stav98/EEKYP/Subsystem1_Irrigation/software/avr/readme.md

Εδώ υπάρχει όλος ο πηγαίος κώδικας για την πλακέτα του Arduino Nano.
IDE VsCode, PlatformIO
