stav98/EEKYP/Subsystem1_Irrigation/software/esp8266/readme.md

Εδώ υπάρχει όλος ο πηγαίος κώδικας για την πλακέτα ESP01 με τον ESP8266.
Η μνήμη flash χωρίζεται σε δύο μέρη. Το 1ο έχει το firmware ενώ το 2ο είναι το filesystem σε LittleFS για ανέβασμα των αρχείων HTML.
IDE VsCode, PlatformIO
