stav98/EEKYP/Subsystem1_Irrigation/3D/valve_body.jpg

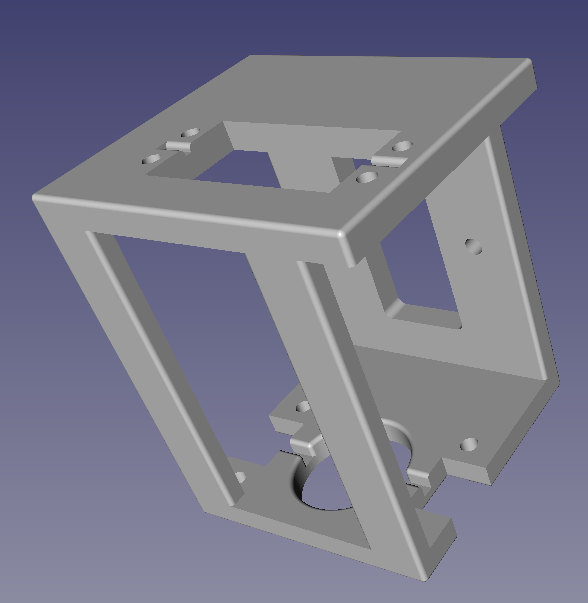
Subsystem1_Irrigation/3D/valve_body.jpg
