stav98/EEKYP/Subsystem1_Irrigation/3D/valve_rotor.jpg

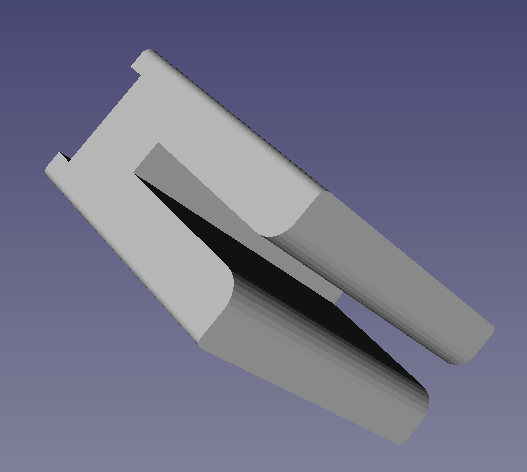
Subsystem1_Irrigation/3D/valve_rotor.jpg
