stav98/EEKYP/Subsystem1_Irrigation/Images/EEKYP1_scr1.png

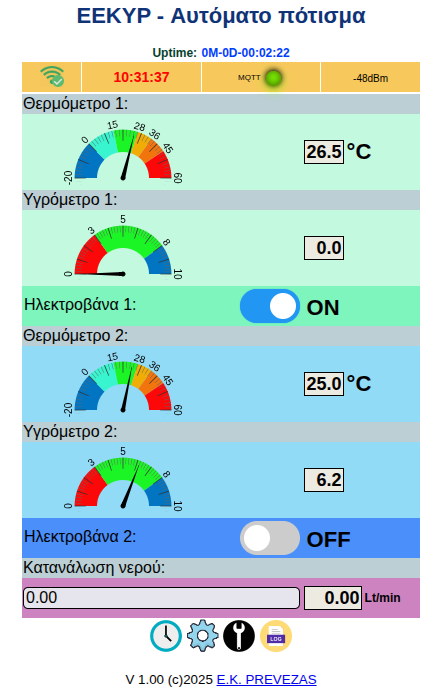
Subsystem1_Irrigation/Images/EEKYP1_scr1.png
