stav98/EEKYP/Subsystem1_Irrigation/Images/EEKYP_team.jpg

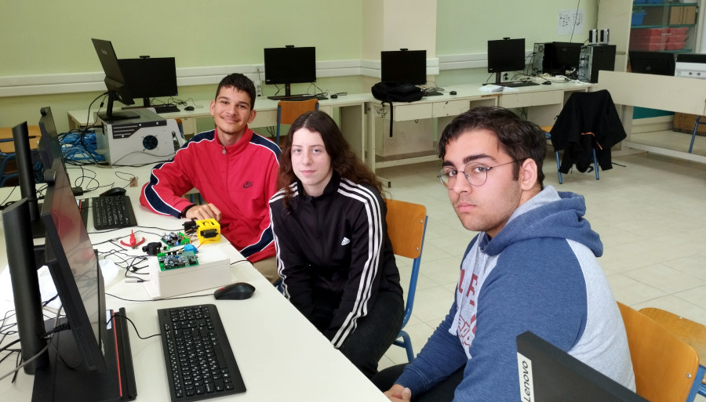
Subsystem1_Irrigation/Images/EEKYP_team.jpg
