stav98/EEKYP/Subsystem1_Irrigation/schematics/Soil-Moisture-Sensor-Module-Schematic.png

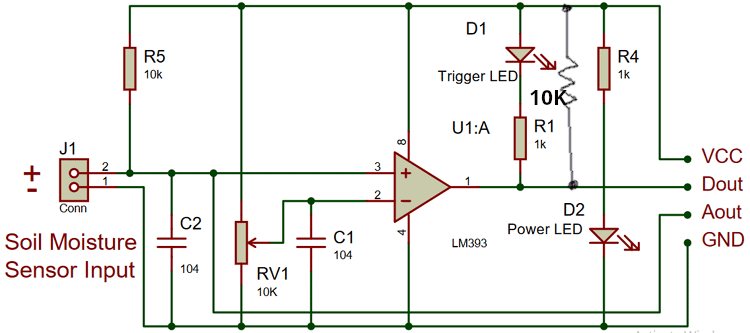
Subsystem1_Irrigation/schematics/Soil-Moisture-Sensor-Module-Schematic.png
