stav98/EEKYP/Subsystem2_PowerSaving/Images/EEKYP2_scr1.png

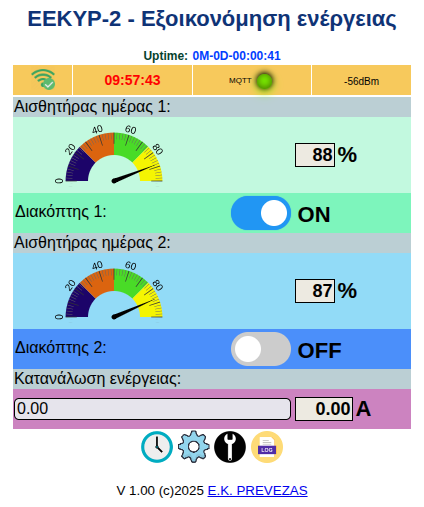
Subsystem2_PowerSaving/Images/EEKYP2_scr1.png
