stav98/EEKYP/Subsystem2_PowerSaving/Images/EEKYP2_scr3.png

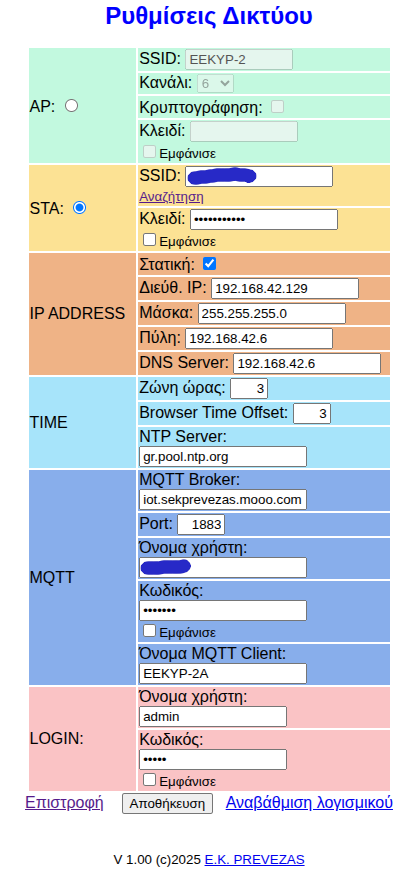
Subsystem2_PowerSaving/Images/EEKYP2_scr3.png
