stav98/EEKYP/Subsystem2_PowerSaving/schematics/current-sensor-circuit.jpg

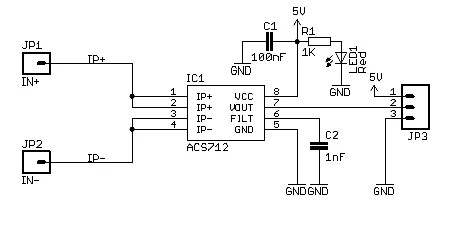
Subsystem2_PowerSaving/schematics/current-sensor-circuit.jpg
