stav98/EEKYP/Subsystem3_WeatherStation/3D/Rainfall meter _ Rain gauge/images/2cdfe765d356b9783a792a951a1a0e3f.png

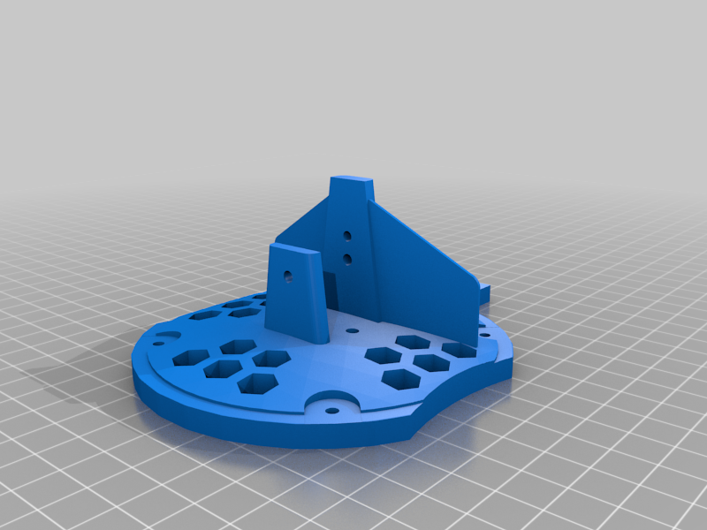
Subsystem3_WeatherStation/3D/Rainfall meter _ Rain gauge/images/2cdfe765d356b9783a792a951a1a0e3f.png
