stav98/EEKYP/Subsystem3_WeatherStation/3D/Rainfall meter _ Rain gauge/images/3b38dc10710fc57b048369caf85057be.png

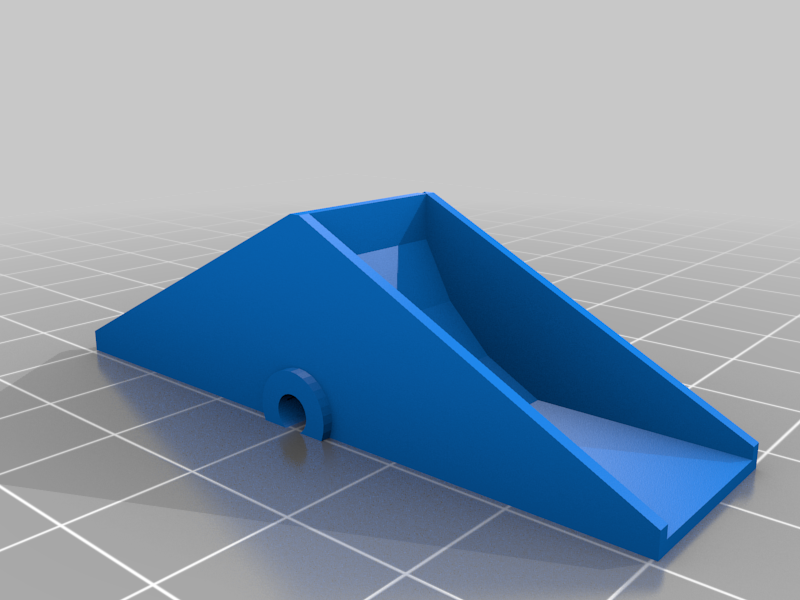
Subsystem3_WeatherStation/3D/Rainfall meter _ Rain gauge/images/3b38dc10710fc57b048369caf85057be.png
