stav98/EEKYP/Subsystem3_WeatherStation/3D/Rainfall meter _ Rain gauge/images/668c7d044ce66c4b228c590e39a806a0.png

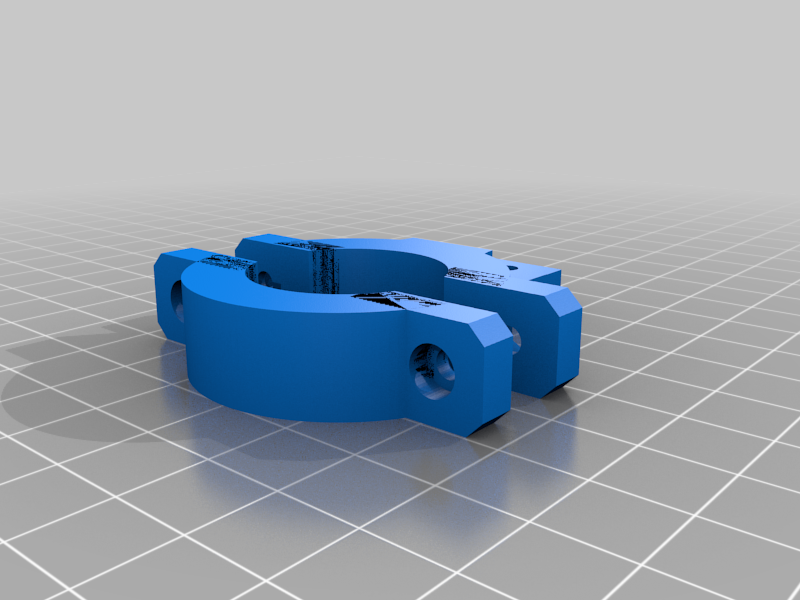
Subsystem3_WeatherStation/3D/Rainfall meter _ Rain gauge/images/668c7d044ce66c4b228c590e39a806a0.png
