stav98/EEKYP/Subsystem3_WeatherStation/3D/Rainfall meter _ Rain gauge/images/2019-07-26_17.47.01.jpg

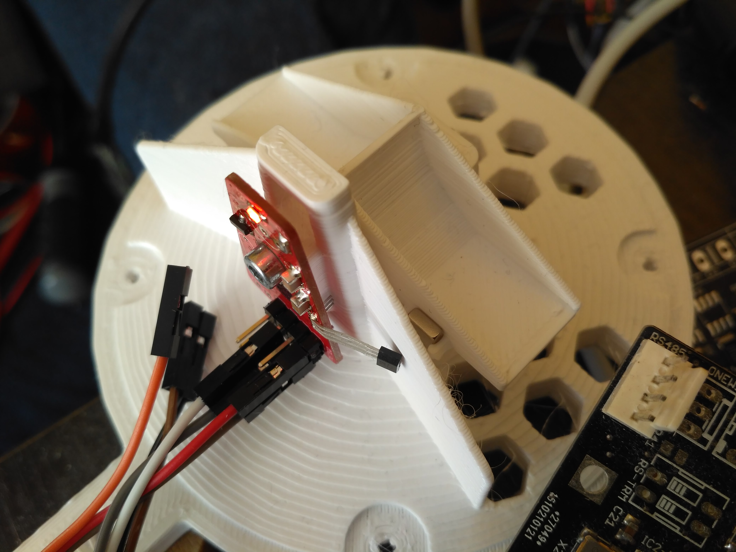
Subsystem3_WeatherStation/3D/Rainfall meter _ Rain gauge/images/2019-07-26_17.47.01.jpg
