stav98/EEKYP/Subsystem3_WeatherStation/3D/Rainfall meter _ Rain gauge/images/2019-07-28_15.31.44.jpg

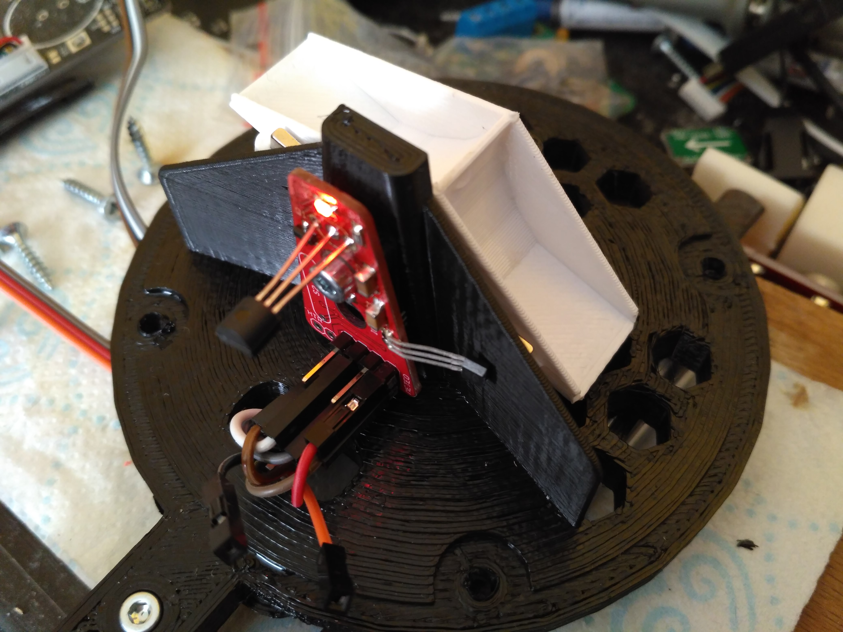
Subsystem3_WeatherStation/3D/Rainfall meter _ Rain gauge/images/2019-07-28_15.31.44.jpg
