stav98/EEKYP/Subsystem3_WeatherStation/3D/Rainfall meter _ Rain gauge/images/2019-07-29_14.39.09.jpg

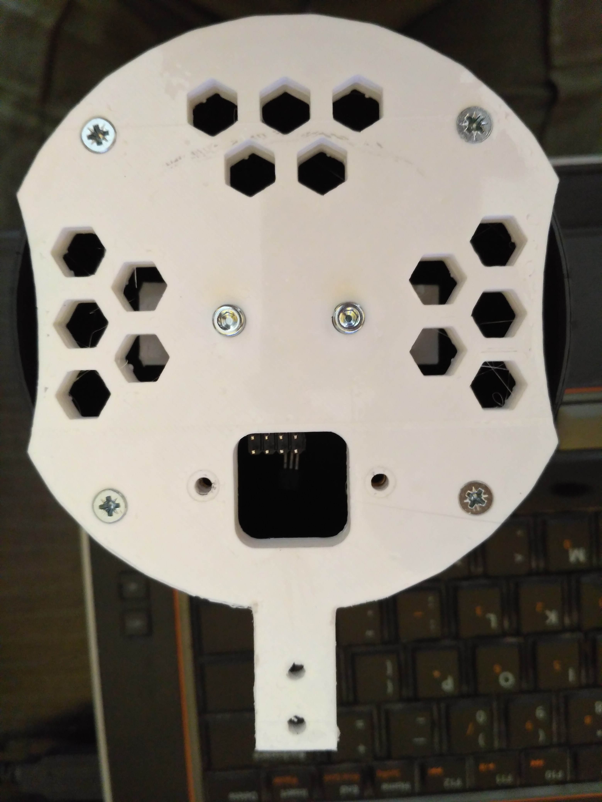
Subsystem3_WeatherStation/3D/Rainfall meter _ Rain gauge/images/2019-07-29_14.39.09.jpg
