stav98/EEKYP/Subsystem3_WeatherStation/3D/Rainfall meter _ Rain gauge/images/2019-07-29_18.38.01.jpg

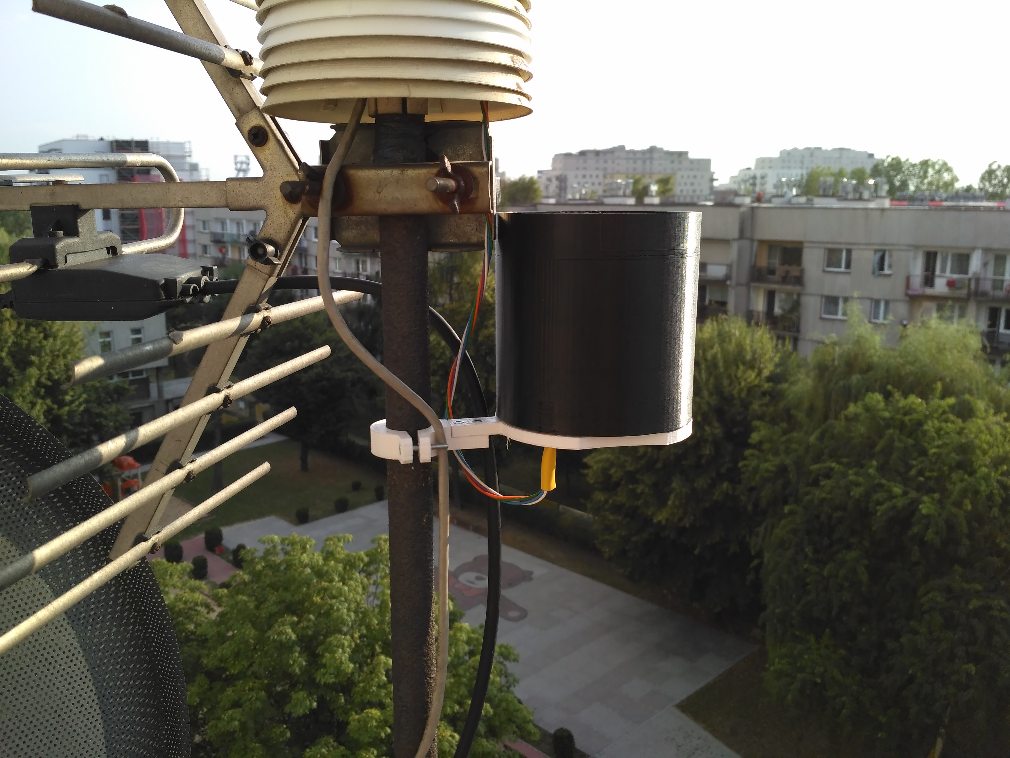
Subsystem3_WeatherStation/3D/Rainfall meter _ Rain gauge/images/2019-07-29_18.38.01.jpg
