stav98/EEKYP/Subsystem3_WeatherStation/3D/Rainfall meter _ Rain gauge/images/7200743348170216a2c66e8219aefd83.png

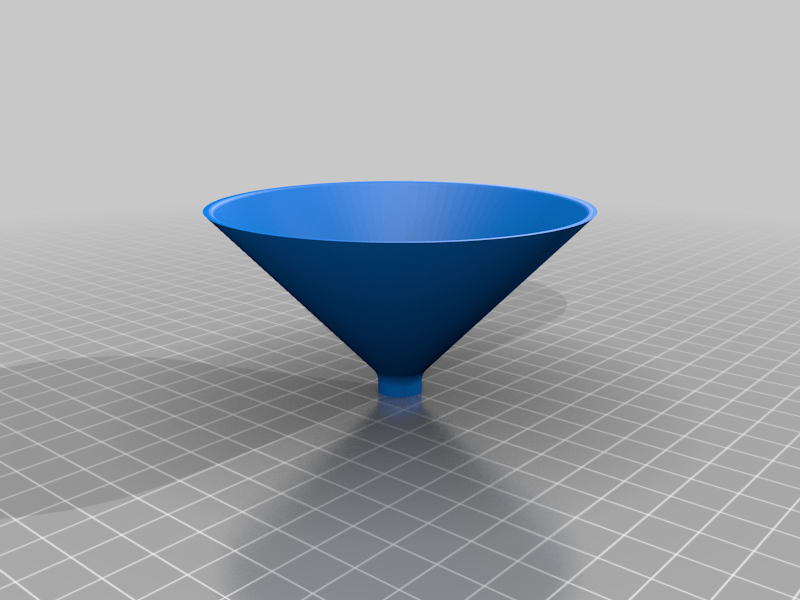
Subsystem3_WeatherStation/3D/Rainfall meter _ Rain gauge/images/7200743348170216a2c66e8219aefd83.png
