stav98/EEKYP/Subsystem3_WeatherStation/3D/Rainfall meter _ Rain gauge/images/Screenshot_2019-07-30_09.27.33.png

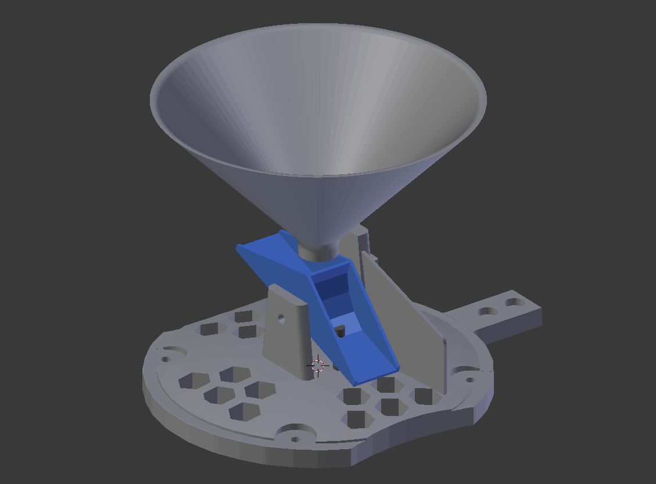
Subsystem3_WeatherStation/3D/Rainfall meter _ Rain gauge/images/Screenshot_2019-07-30_09.27.33.png
