stav98/EEKYP/Subsystem3_WeatherStation/images/weather_system2.jpg

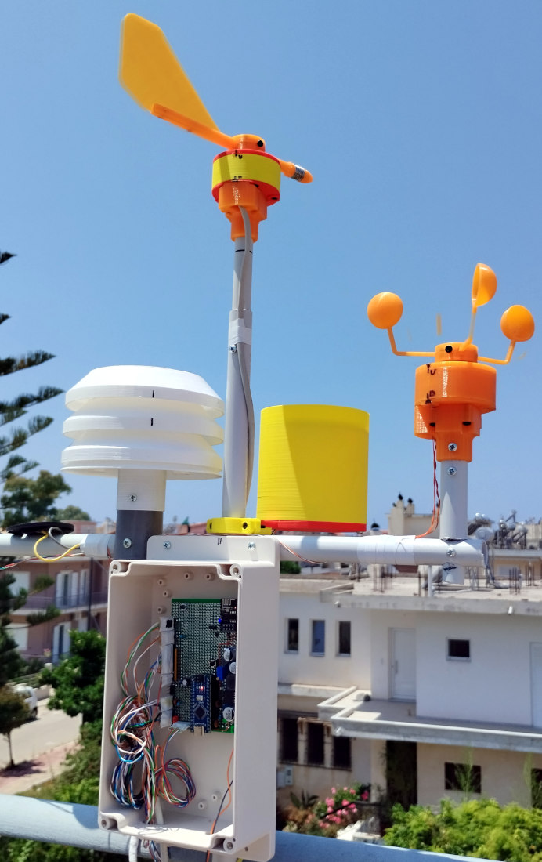
Subsystem3_WeatherStation/images/weather_system2.jpg
