stav98/EEKYP/Subsystem4_NodeRed/images/EEKYP4_S2_scr1.png

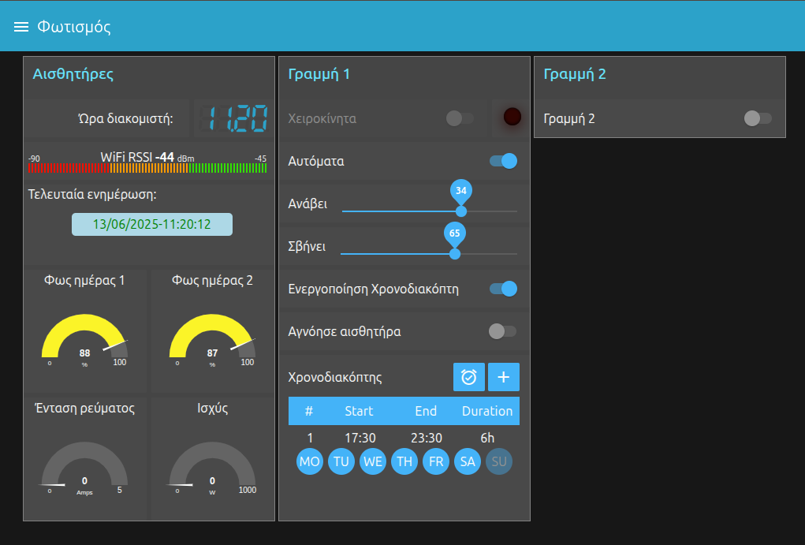
Subsystem4_NodeRed/images/EEKYP4_S2_scr1.png
