stav98/EEKYP/Subsystem3_WeatherStation/3D/Rainfall meter _ Rain gauge/files/pole-holder.stl

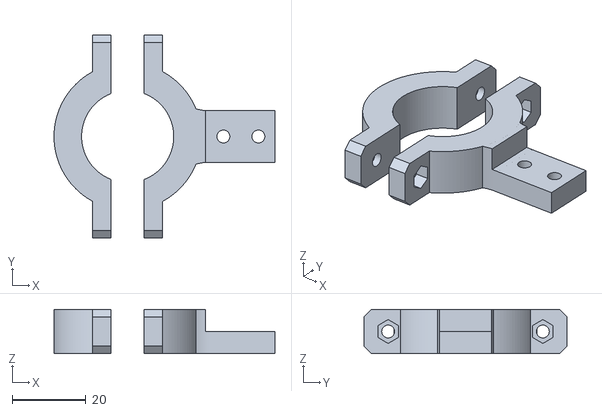
[picture p95: CAD file, 2025-05-21]
Subsystem3_WeatherStation/3D/Rainfall meter _ Rain gauge/files/pole-holder.stl
60.0 x 55.0 x 12.0
