stav98/EEKYP/Subsystem3_WeatherStation/3D/Wind_vane/8_led_holder(x2).STL

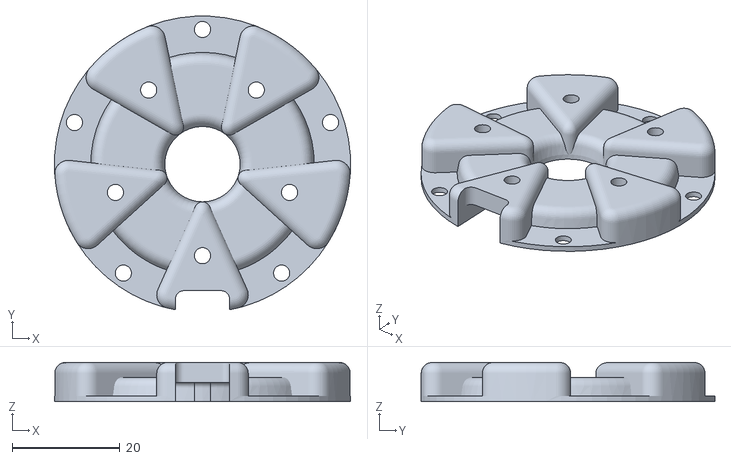
[picture p96: CAD file, 2025-03-21]
Subsystem3_WeatherStation/3D/Wind_vane/8_led_holder(x2).STL
55.0 x 54.5 x 7.25
