stav98/EEKYP/Subsystem3_WeatherStation/3D/Anemometer - 41367/files/body_bottom.STL

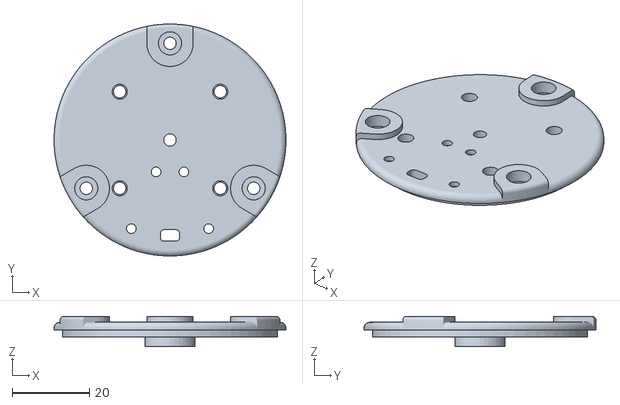
[picture p97: CAD file, 2025-03-21]
Subsystem3_WeatherStation/3D/Anemometer - 41367/files/body_bottom.STL
60.0 x 60.0 x 7.80
