stav98/EEKYP/Subsystem3_WeatherStation/3D/Rainfall meter _ Rain gauge/files/rainfall-meter-bucket-mag.stl

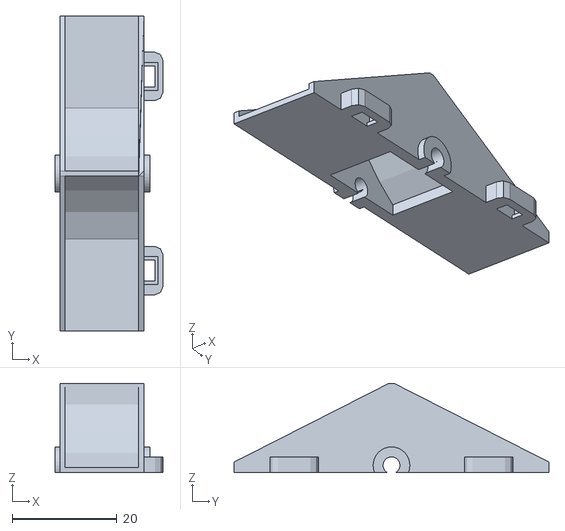
[picture p98: CAD file, 2025-05-21]
Subsystem3_WeatherStation/3D/Rainfall meter _ Rain gauge/files/rainfall-meter-bucket-mag.stl
20.5 x 60.0 x 17.0
