stav98/EEKYP/Subsystem3_WeatherStation/3D/Wind_vane/2_body_top.STL

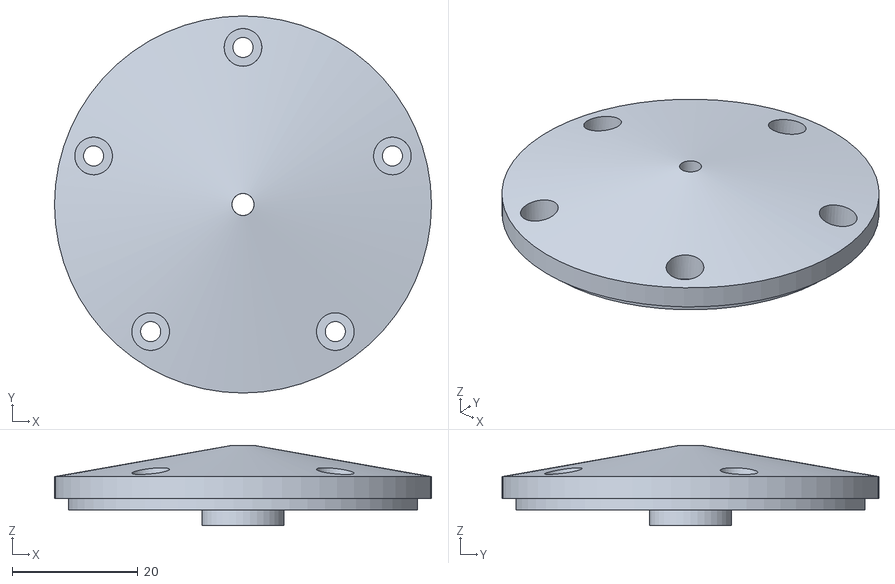
[picture p99: CAD file, 2025-03-21]
Subsystem3_WeatherStation/3D/Wind_vane/2_body_top.STL
60.0 x 60.0 x 12.8
