stav98/EEKYP/Subsystem3_WeatherStation/3D/Anemometer - 41367/files/cupx3.STL

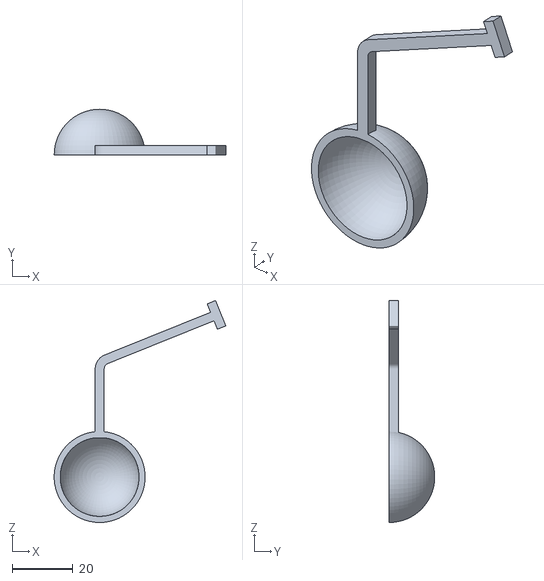
[picture p100: CAD file, 2025-03-21]
Subsystem3_WeatherStation/3D/Anemometer - 41367/files/cupx3.STL
56.6 x 15.0 x 73.2
