stav98/EEKYP/Subsystem3_WeatherStation/3D/Wind_vane/5_noze.STL

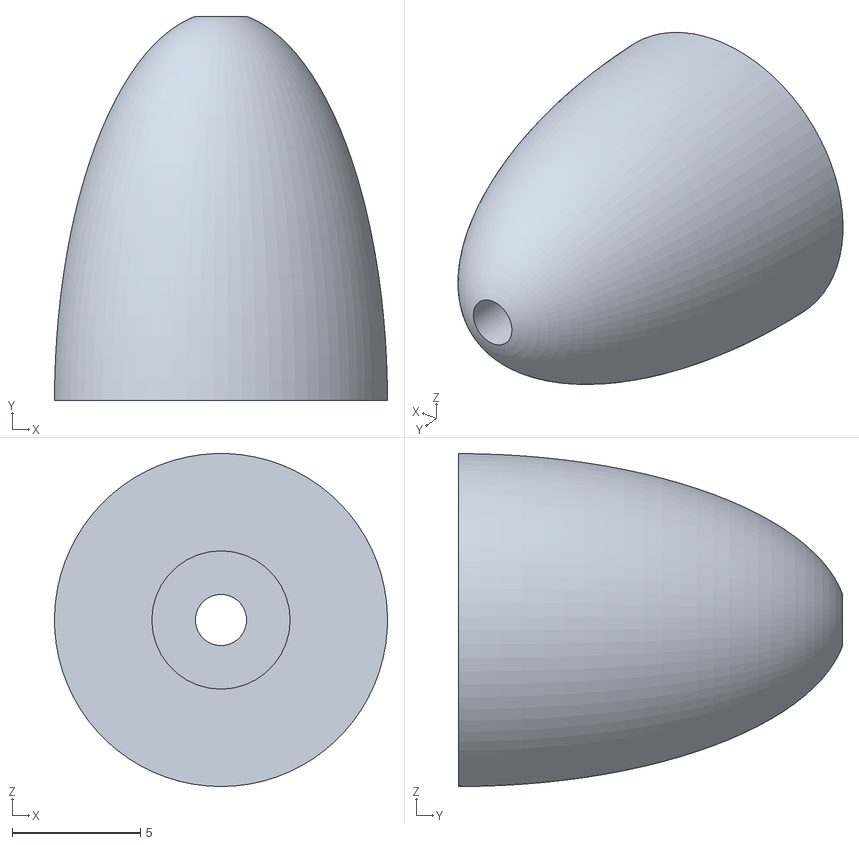
[picture p101: CAD file, 2025-03-21]
Subsystem3_WeatherStation/3D/Wind_vane/5_noze.STL
13.0 x 15.0 x 13.0
