stav98/EEKYP/Subsystem3_WeatherStation/3D/Anemometer - 41367/files/rotor_lockx2.STL

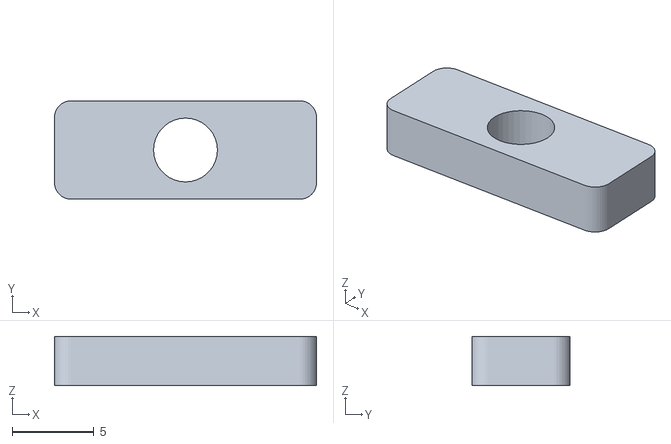
[picture p102: CAD file, 2025-03-21]
Subsystem3_WeatherStation/3D/Anemometer - 41367/files/rotor_lockx2.STL
16.0 x 6.00 x 3.00
