stav98/EEKYP/Subsystem3_WeatherStation/3D/Wind_vane/10_hub_bottom.STL

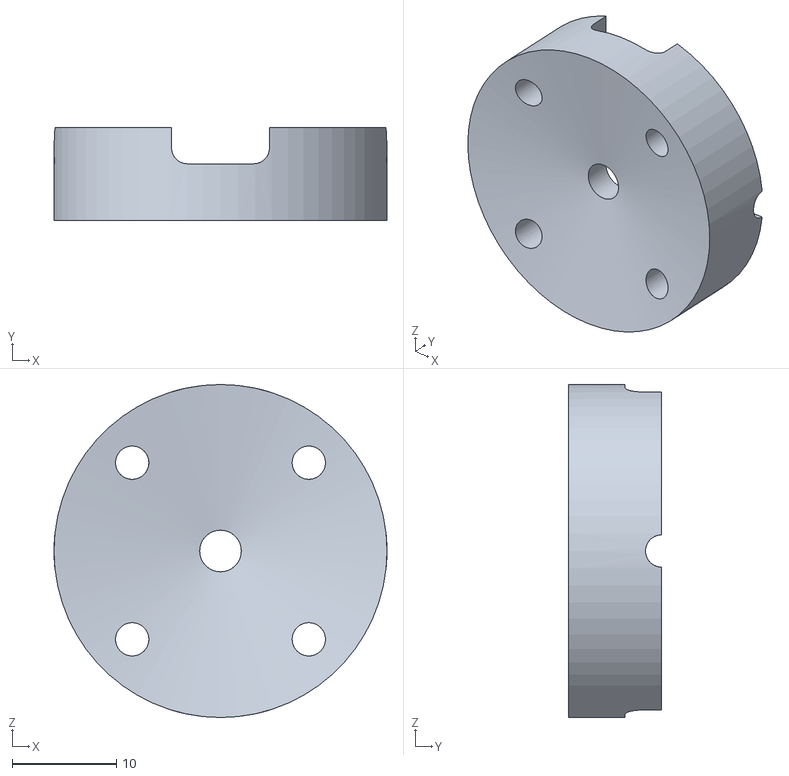
[picture p103: CAD file, 2025-03-21]
Subsystem3_WeatherStation/3D/Wind_vane/10_hub_bottom.STL
32.0 x 8.97 x 32.0
