stav98/EEKYP/Subsystem3_WeatherStation/3D/Wind_vane/9_hub_top.STL

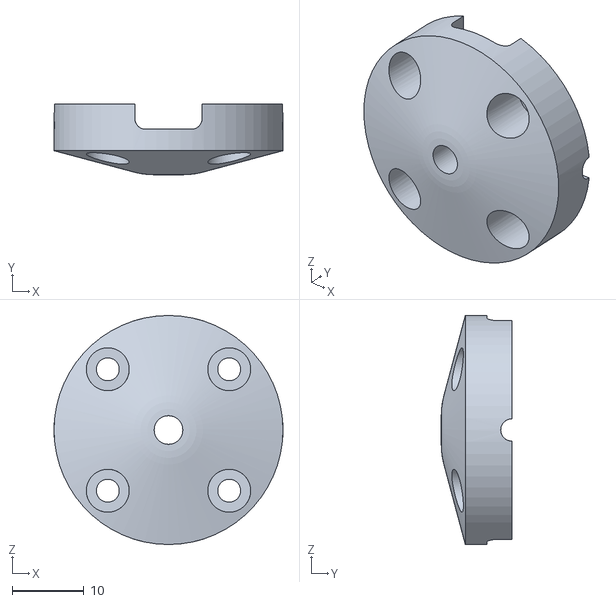
[picture p104: CAD file, 2025-03-21]
Subsystem3_WeatherStation/3D/Wind_vane/9_hub_top.STL
32.0 x 9.87 x 32.0
