stav98/EEKYP/Subsystem3_WeatherStation/3D/Anemometer - 41367/files/rotor_part1.STL

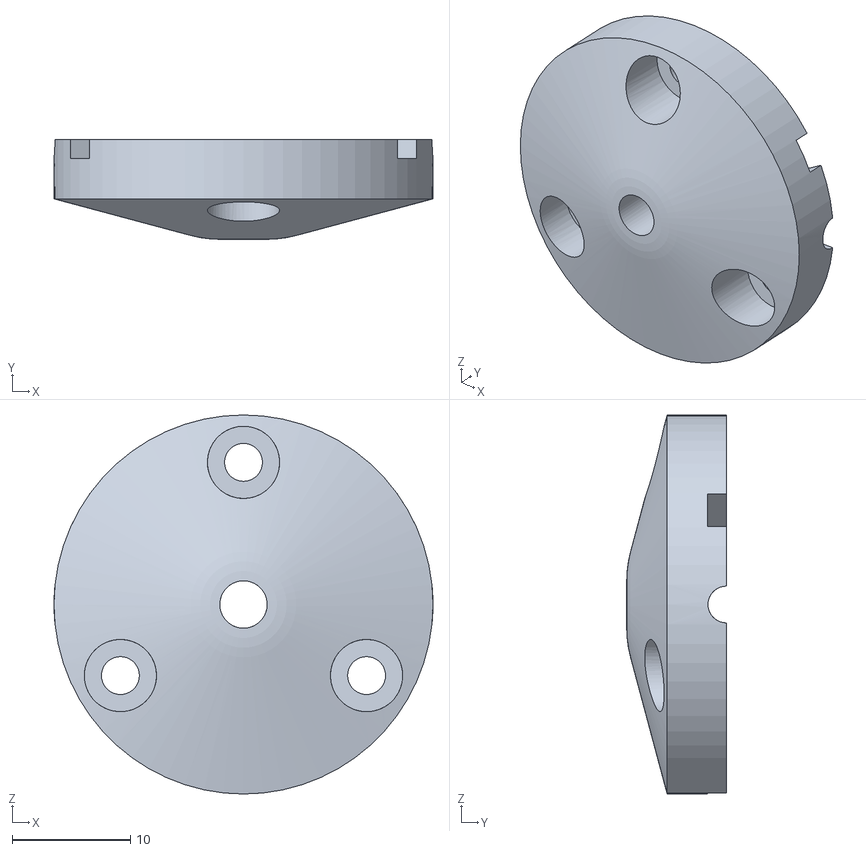
[picture p105: CAD file, 2025-03-21]
Subsystem3_WeatherStation/3D/Anemometer - 41367/files/rotor_part1.STL
32.0 x 8.42 x 32.0
