stav98/EEKYP/Subsystem3_WeatherStation/3D/Wind_vane/4_wheel.STL

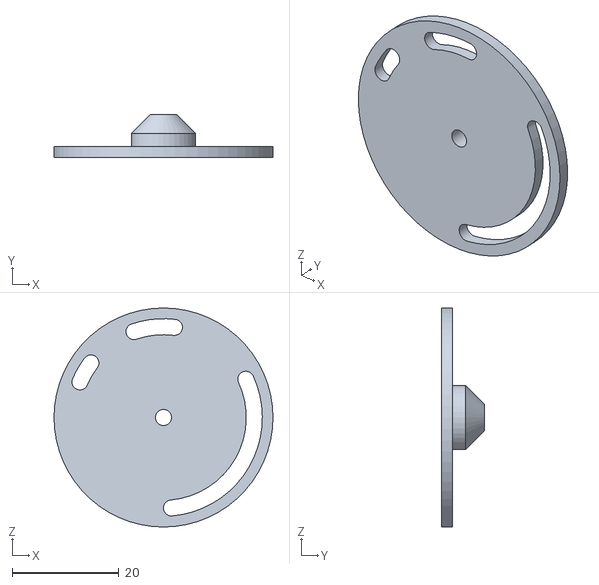
[picture p106: CAD file, 2025-03-21]
Subsystem3_WeatherStation/3D/Wind_vane/4_wheel.STL
41.0 x 8.00 x 41.0
