stav98/EEKYP/Subsystem3_WeatherStation/3D/Anemometer - 41367/files/led_holderx2.STL

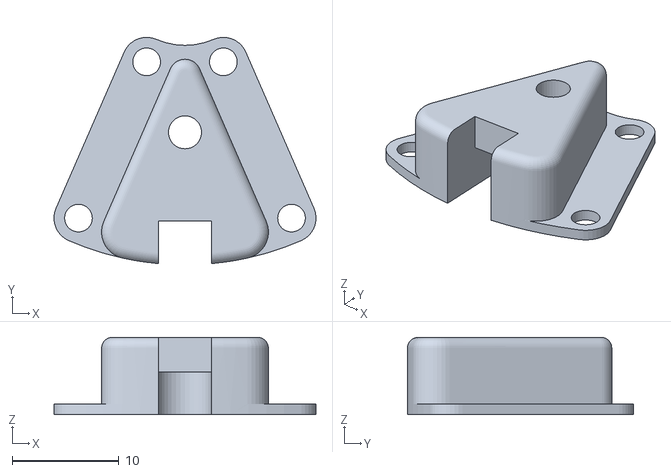
[picture p107: CAD file, 2025-03-21]
Subsystem3_WeatherStation/3D/Anemometer - 41367/files/led_holderx2.STL
24.6 x 21.2 x 7.25
