stav98/EEKYP/Subsystem3_WeatherStation/3D/Wind_vane/3_body_bottom.STL

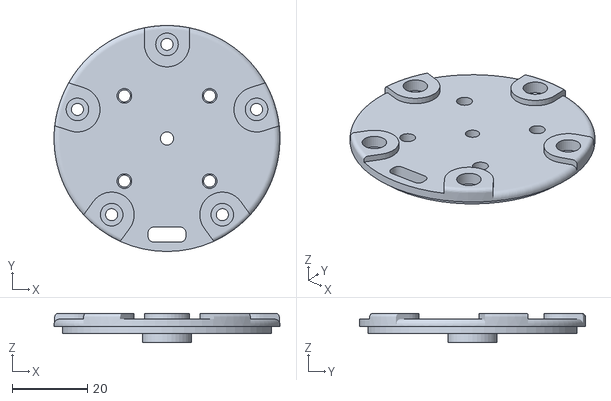
[picture p108: CAD file, 2025-03-21]
Subsystem3_WeatherStation/3D/Wind_vane/3_body_bottom.STL
60.0 x 60.0 x 7.80
