stav98/EEKYP/Subsystem3_WeatherStation/3D/Wind_vane/How to measure wind_ (part 2)_files/fleche_complete_1.jpg

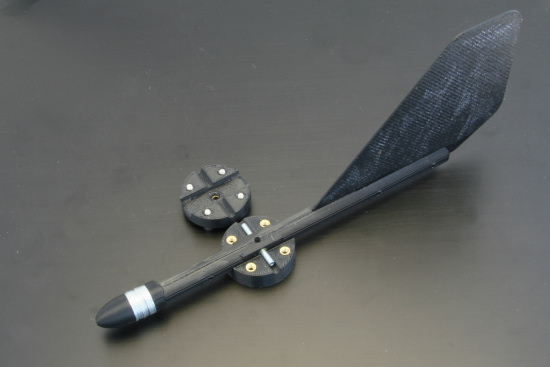
Subsystem3_WeatherStation/3D/Wind_vane/How to measure wind_ (part 2)_files/fleche_complete_1.jpg
