stav98/EEKYP/Subsystem3_WeatherStation/3D/Wind_vane/How to measure wind_ (part 2)_files/girouette_wiring_1.png

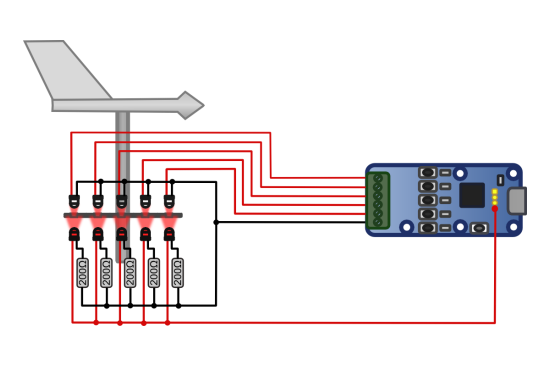
Subsystem3_WeatherStation/3D/Wind_vane/How to measure wind_ (part 2)_files/girouette_wiring_1.png
