stav98/EEKYP/Subsystem3_WeatherStation/3D/Wind_vane/How to measure wind_ (part 2)_files/inserts_3.jpg

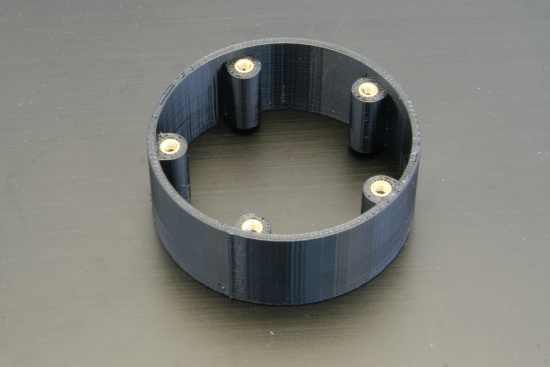
Subsystem3_WeatherStation/3D/Wind_vane/How to measure wind_ (part 2)_files/inserts_3.jpg
