stav98/EEKYP/Subsystem3_WeatherStation/images/anemometer_assembled.jpg

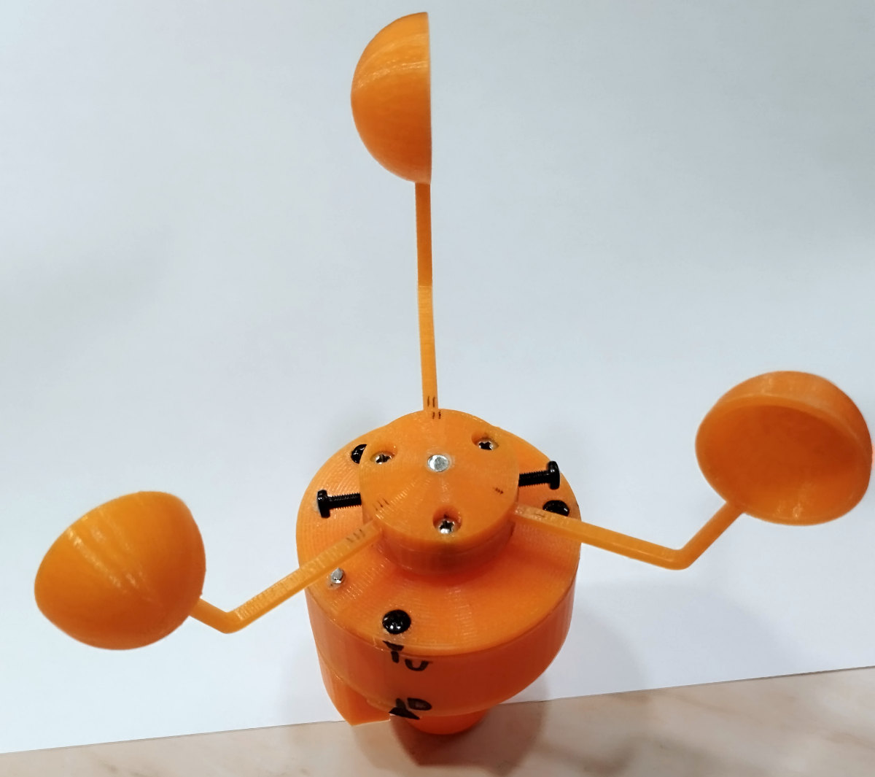
Subsystem3_WeatherStation/images/anemometer_assembled.jpg
