stav98/EEKYP/Subsystem3_WeatherStation/software/avr/EEKYP3_AVR/src/buttons.h

#define PULL_UP     HIGH
void SetupButtons(void);
void But_Click(void);
void But_Long_Click(void);
void But_Dbl_Click(void);

class Buttons
{
 private:
   int _pin;

    // Properties //
   ////////////////

   // Debounce period to prevent flickering when pressing or releasing the button (in ms)
   int Debounce;
   // Max period between clicks for a double click event (in ms)
   int DblClickDelay;
   // Hold period for a long press event (in ms)
   int LongPressDelay;

    // Variables //
   ///////////////

   // Value read from button
   boolean state;
   // Last value of button state
   boolean _lastState;
   // whether we're waiting for a double click (down)
   boolean _dblClickWaiting;
   // whether to register a double click on next release, or whether to wait and click
   boolean _dblClickOnNextUp;
   // whether it's OK to do a single click
   boolean _singleClickOK;

   // time the button was pressed down
   long _downTime;
   // time the button was released
   long _upTime;

   // whether to ignore the button release because the click+hold was triggered
   boolean _ignoreUP;
   // when held, whether to wait for the up event
   boolean _waitForUP;
   // whether or not the hold event happened already
   boolean _longPressHappened;

 public:
   void (*OnClick)(void);
   void (*OnDblClick)(void);
   void (*OnLongPress)(void);

 Buttons()
     {
      // Initialization of properties
      Debounce = 30;
      DblClickDelay = 300; //300
      LongPressDelay = 5000;

      // Initialization of variables
      state = true;
      _lastState = true;
      _dblClickWaiting = false;
      _dblClickOnNextUp = false;
      _singleClickOK = false; //Default = true
      _downTime = -1;
      _upTime = -1;
      _ignoreUP = false;
      _waitForUP = false;
      _longPressHappened = false;
     }

   void Configure(int pin)
      {
       _pin = pin;
       pinMode(_pin, INPUT_PULLUP); //Κάνε το pin είσοδο Pull Up
      }

   void CheckBP(void)
      {
       int resultEvent = 0;
       long millisRes = millis();
       state = digitalRead(_pin);
       //---- Κουμπί πατήθηκε ----
       if (state != PULL_UP && _lastState == PULL_UP  && (millisRes - _upTime) > Debounce)
          {
           //Serial.println("button down"); //Debug
           _downTime = millisRes;
           _ignoreUP = false;
           _waitForUP = false;
           _singleClickOK = true;
           _longPressHappened = false;
           if ((millisRes - _upTime) < DblClickDelay && _dblClickOnNextUp == false && _dblClickWaiting == true)
               _dblClickOnNextUp = true;
           else
               _dblClickOnNextUp = false;
           _dblClickWaiting = false;
          }
       // Button released
       else if (state == PULL_UP && _lastState != PULL_UP && (millisRes - _downTime) > Debounce)
          {
           //Serial.println("button up");
           if (_ignoreUP == false) //Replace "(!_ignoreUP)" by "(not _ignoreUP)"
              {
               _upTime = millisRes;
               if (_dblClickOnNextUp == false)
                   _dblClickWaiting = true;
               else
                  {
                   resultEvent = 2;
                   _dblClickOnNextUp = false;
                   _dblClickWaiting = false;
                   _singleClickOK = false;
                  }
              }
          }

       // Test for normal click event: DblClickDelay expired
       if (state == PULL_UP && (millisRes - _upTime) >= DblClickDelay && _dblClickWaiting == true && _dblClickOnNextUp == false && _singleClickOK == true && resultEvent != 2)
          {
           resultEvent = 1;
           _dblClickWaiting = false;
          }

       //----- Έλεγχος για παρατεταμένο πάτημα -----
       //Είναι πατημένο και ο χρόνος πέρασε την καθυστέρηση του LongPressDelay
       if (state != PULL_UP && (millisRes - _downTime) >= LongPressDelay)
          {
           //Πυροδότησε το παρατεταμένο πάτημα
           // Αν δεν πατήθηκε πριν παρατεταμένα
           if (_longPressHappened == false)
              {
               resultEvent = 3;
               _waitForUP = true;
               _ignoreUP = true;
               _dblClickOnNextUp = false;
               _dblClickWaiting = false;
               _downTime = millis(); //ισως δεν χρειάζεται
               _longPressHappened = true;
              }
          }
       _lastState = state;
       //if (resultEvent!=0)
       //  Serial.println((String)"resultEvent: " + (String) resultEvent);

       if (resultEvent == 1 && OnClick) OnClick();
       if (resultEvent == 2 && OnDblClick) OnDblClick();
       if (resultEvent == 3 && OnLongPress) OnLongPress();
       //  if (resultEvent != 0)
       //    Usb.println(resultEvent);
      } //Τέλος της CheckBP()
};  //Τέλος ορισμού της κλάσης

Buttons but_prog;

void SetupButtons()
{
 but_prog.Configure(BUTTON1);
 but_prog.OnClick = But_Click;
 but_prog.OnLongPress = But_Long_Click;
 but_prog.OnDblClick = But_Dbl_Click;
}

//Όταν πατιέται ένα κλικ στο button
void But_Click()
{
 Serial.println("Button Click"); //Debug
}

//Όταν πατιέται παρατεταμένα
void But_Long_Click()
{
 //Serial.println("Button Long Click"); //Debug
 if (Serial1.available() == 0) Serial1.println(F("defaults"));
}

//Όταν πατιέται διπλό κλικ
void But_Dbl_Click()
{
 Serial.println("Button Double Click"); //Debug
}
